orcular-org/orcuDispenser/Documentation/images/readme/dispenser_white+blue_1-min.png

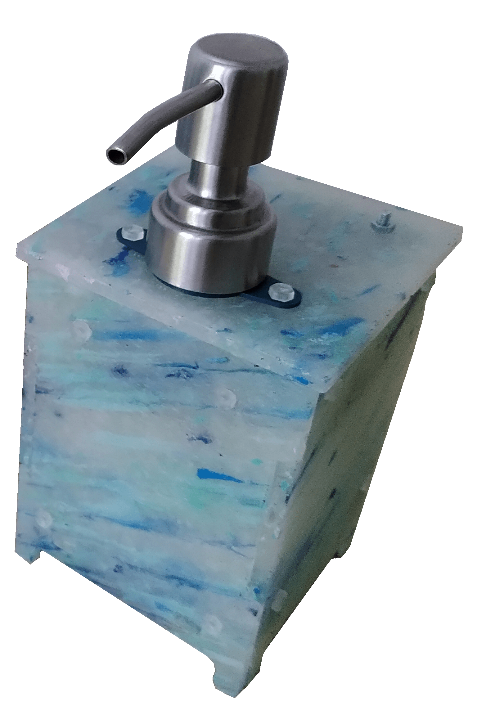
Documentation/images/readme/dispenser_white+blue_1-min.png
