orcular-org/orcuDispenser/Documentation/images/Assembly/11B_Angle_top.PNG

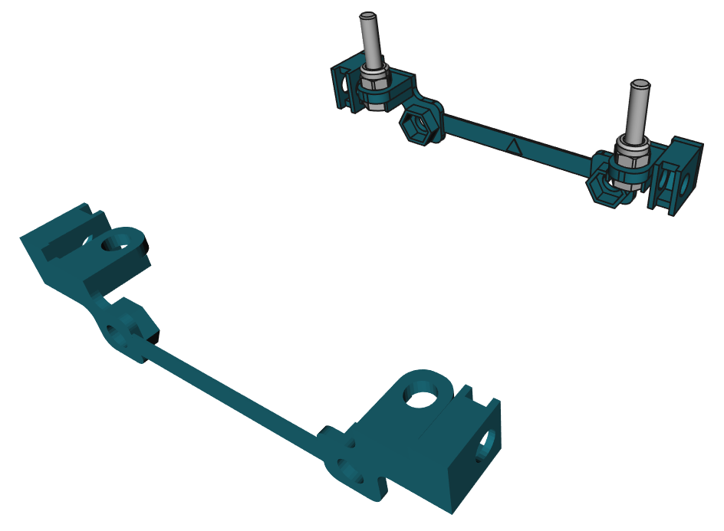
Documentation/images/Assembly/11B_Angle_top.PNG
