orcular-org/orcuDispenser/Documentation/images/Assembly/Locknut.PNG

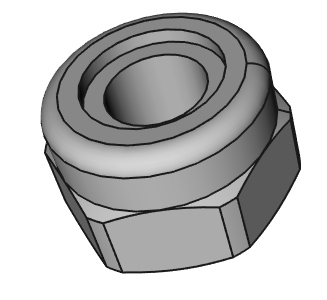
Documentation/images/Assembly/Locknut.PNG
