orcular-org/orcuDispenser/Documentation/images/Assembly/Screw_PP.PNG

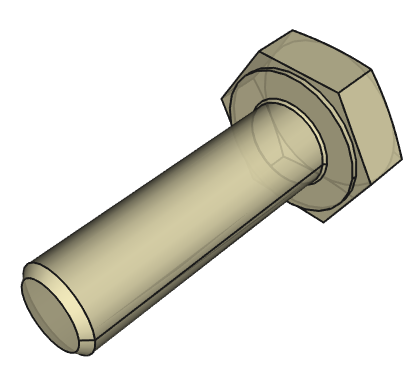
Documentation/images/Assembly/Screw_PP.PNG
